calebhabesh/doorlink/main/services/connectivity_manager.hpp

#pragma once

#include <atomic>
#include <cstdint>

#include "esp_err.h"
#include "services/camera_service.hpp"
#include "services/audio_service.hpp"

namespace doorbell {

class ConnectivityManager final {
public:
    ConnectivityManager() = default;
    ~ConnectivityManager();

    ConnectivityManager(const ConnectivityManager &) = delete;
    ConnectivityManager &operator=(const ConnectivityManager &) = delete;

    esp_err_t connect(int timeout_ms = 0);
    esp_err_t trigger(const char *event_id, const char *event_type,
                      const char *device_id,
                      const char *firmware_version,
                      bool dispatch_alerts,
                      int timeout_ms = 0) const;
    esp_err_t upload(const CapturedImage *image, const RecordedAudio *audio,
                     const char *event_type,
                     const char *event_id, const char *device_id,
                     const char *firmware_version,
                     int timeout_ms = 0) const;
    esp_err_t shutdown();
    esp_err_t close_session(const char *session_id, int timeout_ms = 5000) const;
    esp_err_t complete_press(const char *press_id, std::uint32_t duration_ms,
                             int timeout_ms = 5000) const;
    void set_battery_millivolts(std::uint32_t millivolts)
    {
        battery_millivolts_.store(millivolts);
    }
    bool connected() const { return connected_.load(); }

private:
    std::atomic_bool connected_{false};
    std::atomic_uint32_t battery_millivolts_{0};
};

}  // namespace doorbell
