calebhabesh/doorlink/main/chime_player.h

#pragma once

#include <stdbool.h>

#include "esp_err.h"
#include "freertos/FreeRTOS.h"

#ifdef __cplusplus
extern "C" {
#endif

/**
 * @brief Play the embedded doorbell chime sound asynchronously in a background task.
 * @return ESP_OK on task creation success, or error code.
 */
esp_err_t chime_player_play_async(void);

/**
 * @brief Play an interruptible repress chime only if the I2S bus is idle.
 *
 * Unlike the first-press chime, this request never waits behind microphone or
 * homeowner playback. If another local chime is already audible, its existing
 * I2S stream is rewound at the next PCM chunk boundary so every physical press
 * receives prompt audible acknowledgement.
 *
 * @return ESP_OK when playback was started, retriggered, or intentionally
 * suppressed; ESP_ERR_NO_MEM when the playback task could not be created.
 */
esp_err_t chime_player_play_repress_async(void);

/**
 * @brief Play the embedded doorbell chime sound synchronously (blocking until finished).
 * @return ESP_OK on playback success, or error code.
 */
esp_err_t chime_player_play_sync(void);

/**
 * @brief Check if local chime playback (or retrigger window) is currently active.
 * @return true if currently playing or retriggering, false if idle.
 */
bool chime_player_is_playing(void);

/**
 * @brief Check whether the active chime may yield to visitor/homeowner audio.
 */
bool chime_player_is_interruptible(void);

/**
 * @brief Confirm AMP_EN belongs to the bounded low-power camera overlap path.
 */
bool chime_player_camera_overlap_active(void);

/**
 * @brief Select the bounded low-power chime profile around camera use.
 *
 * An already-active full chime may finish before startup. New requests use the
 * normal doorbell waveform at the configured low overlap gain and may continue
 * while U9 starts.
 */
void chime_player_set_camera_overlap_mode(bool enabled);

/**
 * @brief Wait until the amplifier has been muted and chime playback released.
 * @return ESP_OK when idle, ESP_ERR_TIMEOUT if timeout_ticks elapsed first.
 */
esp_err_t chime_player_wait_until_idle(TickType_t timeout_ticks);

/**
 * @brief Ask the asynchronous chime to stop at the next PCM chunk boundary.
 *
 * The amplifier is muted and the shared I2S bus is released before playback
 * finishes. Safe to call when no chime is active.
 */
void chime_player_request_stop(void);

#ifdef __cplusplus
}
#endif
