calebhabesh/doorlink/main/doorbell_chime_pcm.h

#pragma once

#include <stddef.h>
#include <stdint.h>

#ifdef __cplusplus
extern "C" {
#endif

extern const uint32_t g_doorbell_chime_pcm_len;
extern const uint8_t g_doorbell_chime_pcm[];

#ifdef __cplusplus
}
#endif
