calebhabesh/doorlink/main/config.example.h

#pragma once

// ==========================================
// WiFi Configuration
// ==========================================
#define WIFI_SSID       "YOUR_WIFI_SSID"
#define WIFI_PASSWORD   "YOUR_WIFI_PASSWORD"
#define WIFI_MAX_RETRY  5

// Optional Static IP Configuration for sub-300ms Wi-Fi connection
// #define WIFI_STATIC_IP   "192.168.1.20"
// #define WIFI_NETMASK     "255.255.255.0"
// #define WIFI_GATEWAY     "192.168.1.1"
// #define WIFI_DNS         "192.168.1.1"
// #define WIFI_CHANNEL     6

// ==========================================
// MQTT Configuration
// ==========================================
// Replace with the IP address of your Raspberry Pi 4 running the Mosquitto broker
#define MQTT_BROKER_URI "mqtt://192.168.1.10:1883"
#define MQTT_PTT_TOPIC  "doorbell/commands/audio"
// Optional broker credentials. Intercom commands are independently HMAC-signed
// with GATEWAY_API_KEY, but broker authentication remains useful defense in depth.
// #define MQTT_USERNAME "front-door"
// #define MQTT_PASSWORD "YOUR_MQTT_PASSWORD"

// ==========================================
// Gateway Configuration
// ==========================================
// Replace with the IP address of your Raspberry Pi running the Spring Boot Gateway
#define GATEWAY_API_URL "http://192.168.1.10:8080/api/events"
// Use the exact same high-entropy value as gateway.api.key/GATEWAY_API_KEY on
// the Raspberry Pi. It authenticates HTTP requests and signed MQTT commands.
#define GATEWAY_API_KEY "YOUR_HARD_TO_GUESS_API_KEY"
#define DEVICE_ID       "front-door"

// ==========================================
// Media Configuration
// ==========================================
#define AUDIO_RECORD_TIME_SEC 5
